MKrysz/POV_Display/POV_display_code/Core/Inc/clk.h

#ifndef A386B258_FA04_44B2_AE7A_AE9C989B530D
#define A386B258_FA04_44B2_AE7A_AE9C989B530D

const uint8_t hours[8] = {0b00000000, 0b00000000, 0b00000000, 0b00000000, 0b00000000, 0b00100001, 0b01001000, 0b10010010};

const uint8_t minutes[8] = {0b00000000, 0b00000000, 0b00000000, 0b10010010, 0b00100101, 0b01001000, 0b10010010, 0b00100101};

const uint8_t seconds[8] = {0b00100101, 0b01001000, 0b10010010, 0b00100101, 0b01001000, 0b10010010, 0b00100101, 0b01001000};

const uint8_t CLK_BKGD[120][8] = {
{0b00000000, 0b00000000, 0b00000000, 0b00000000, 0b00000000, 0b00000000, 0b00000000, 0b00000000},
{0b11100000, 0b11000001, 0b00000000, 0b00000000, 0b00000000, 0b00000000, 0b00000000, 0b00000000},
{0b00011100, 0b11111001, 0b00000000, 0b00000000, 0b00000000, 0b00000000, 0b00000000, 0b00000000},
{0b00011101, 0b11000111, 0b00000000, 0b00000000, 0b00000000, 0b00000000, 0b00000000, 0b00000000},
{0b11100000, 0b11000001, 0b00000000, 0b00000000, 0b00000000, 0b00000000, 0b00000000, 0b00000000},
{0b00000000, 0b00000000, 0b00000000, 0b00000000, 0b00000000, 0b00000000, 0b00000000, 0b00000000},
{0b00000000, 0b00000000, 0b00000000, 0b00000000, 0b00000000, 0b00000000, 0b00000000, 0b00000000},
{0b00000000, 0b00000000, 0b00000000, 0b00000000, 0b00000000, 0b00000000, 0b00000000, 0b00000000},
{0b00000000, 0b00000000, 0b00000000, 0b00000000, 0b00000000, 0b00000000, 0b00000000, 0b00000000},
{0b11100000, 0b00000000, 0b00000000, 0b00000000, 0b00000000, 0b00000000, 0b00000000, 0b00000000},
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
{0b00000000, 0b00000000, 0b00000000, 0b00000000, 0b00000000, 0b00000000, 0b00000000, 0b00000000},
{0b11111101, 0b11111111, 0b00000000, 0b00000000, 0b00000000, 0b00000000, 0b00000000, 0b00000000},
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
};



#endif /* A386B258_FA04_44B2_AE7A_AE9C989B530D */
