MKrysz/POV_Display/POV_display_code/Core/Inc/config.h

#ifndef C484BAE8_510C_4F08_8290_32E19870EC4C
#define C484BAE8_510C_4F08_8290_32E19870EC4C

#define MODE_IMAGE
// #define MODE_ANALOG_CLOCK

#define SHUTDOWN_ENABLE 1

#endif /* C484BAE8_510C_4F08_8290_32E19870EC4C */
