MKrysz/POV_Display/POV_display_code/Core/Src/gpio.c

/**
  ******************************************************************************
  * @file    gpio.c
  * @brief   This file provides code for the configuration
  *          of all used GPIO pins.
  ******************************************************************************
  * @attention
  *
  * <h2><center>&copy; Copyright (c) 2022 STMicroelectronics.
  * All rights reserved.</center></h2>
  *
  * This software component is licensed by ST under BSD 3-Clause license,
  * the "License"; You may not use this file except in compliance with the
  * License. You may obtain a copy of the License at:
  *                        opensource.org/licenses/BSD-3-Clause
  *
  ******************************************************************************
  */

/* Includes ------------------------------------------------------------------*/
#include "gpio.h"

/* USER CODE BEGIN 0 */
#include <stdbool.h>
#include "tim.h"
#include "led.h"
#include "array.h"
#include "main.h"
#include "config.h"
/* USER CODE END 0 */

/*----------------------------------------------------------------------------*/
/* Configure GPIO                                                             */
/*----------------------------------------------------------------------------*/
/* USER CODE BEGIN 1 */
/*externs*/
extern volatile uint16_t period;
extern volatile uint16_t periodUS;
extern volatile size_t imgIdx;
extern volatile bool isShutDown;

/*variables*/

volatile bool GPIO_Flag = false;
/* USER CODE END 1 */

/** Configure pins as
        * Analog
        * Input
        * Output
        * EVENT_OUT
        * EXTI
*/
void MX_GPIO_Init(void)
{

  GPIO_InitTypeDef GPIO_InitStruct = {0};

  /* GPIO Ports Clock Enable */
  __HAL_RCC_GPIOC_CLK_ENABLE();
  __HAL_RCC_GPIOA_CLK_ENABLE();
  __HAL_RCC_GPIOB_CLK_ENABLE();

  /*Configure GPIO pin Output Level */
  HAL_GPIO_WritePin(GPIOA, BAT_EN_Pin|NOT_OE_Pin|NOT_CLEAR_Pin, GPIO_PIN_RESET);

  /*Configure GPIO pin Output Level */
  HAL_GPIO_WritePin(RCLK_GPIO_Port, RCLK_Pin, GPIO_PIN_RESET);

  /*Configure GPIO pin : PtPin */
  GPIO_InitStruct.Pin = FDBK_Pin;
  GPIO_InitStruct.Mode = GPIO_MODE_IT_RISING;
  GPIO_InitStruct.Pull = GPIO_NOPULL;
  HAL_GPIO_Init(FDBK_GPIO_Port, &GPIO_InitStruct);

  /*Configure GPIO pins : PAPin PAPin PAPin */
  GPIO_InitStruct.Pin = BAT_EN_Pin|NOT_OE_Pin|NOT_CLEAR_Pin;
  GPIO_InitStruct.Mode = GPIO_MODE_OUTPUT_PP;
  GPIO_InitStruct.Pull = GPIO_NOPULL;
  GPIO_InitStruct.Speed = GPIO_SPEED_FREQ_LOW;
  HAL_GPIO_Init(GPIOA, &GPIO_InitStruct);

  /*Configure GPIO pin : PtPin */
  GPIO_InitStruct.Pin = RCLK_Pin;
  GPIO_InitStruct.Mode = GPIO_MODE_OUTPUT_PP;
  GPIO_InitStruct.Pull = GPIO_NOPULL;
  GPIO_InitStruct.Speed = GPIO_SPEED_FREQ_LOW;
  HAL_GPIO_Init(RCLK_GPIO_Port, &GPIO_InitStruct);

  /*Configure GPIO pin : PtPin */
  GPIO_InitStruct.Pin = USB_FLAG_Pin;
  GPIO_InitStruct.Mode = GPIO_MODE_INPUT;
  GPIO_InitStruct.Pull = GPIO_NOPULL;
  HAL_GPIO_Init(USB_FLAG_GPIO_Port, &GPIO_InitStruct);

  /* EXTI interrupt init*/
  HAL_NVIC_SetPriority(EXTI4_15_IRQn, 0, 0);
  HAL_NVIC_EnableIRQ(EXTI4_15_IRQn);

}

/* USER CODE BEGIN 2 */

void GPIO_Init(){
}

void HAL_GPIO_EXTI_Callback(uint16_t GPIO_Pin){
  GPIO_Flag = true;
  #if SHUTDOWN_ENABLE
  if(isShutDown)
    wakeUpRoutine();
  #endif
  

  periodUS = __HAL_TIM_GET_COUNTER(&HTIM_US_GET);
  __HAL_TIM_SET_COUNTER(&HTIM_US_GET,0);

  // anchor the image
  imgIdx = 0;
}
/* USER CODE END 2 */

/************************ (C) COPYRIGHT STMicroelectronics *****END OF FILE****/
