MKrysz/POV_Display/POV_display_code/Core/Src/rtc.c

/**
  ******************************************************************************
  * @file    rtc.c
  * @brief   This file provides code for the configuration
  *          of the RTC instances.
  ******************************************************************************
  * @attention
  *
  * <h2><center>&copy; Copyright (c) 2022 STMicroelectronics.
  * All rights reserved.</center></h2>
  *
  * This software component is licensed by ST under BSD 3-Clause license,
  * the "License"; You may not use this file except in compliance with the
  * License. You may obtain a copy of the License at:
  *                        opensource.org/licenses/BSD-3-Clause
  *
  ******************************************************************************
  */

/* Includes ------------------------------------------------------------------*/
#include "rtc.h"

RTC_HandleTypeDef hrtc;

/* RTC init function */
void MX_RTC_Init(void)
{

  RTC_TimeTypeDef sTime = {0};
  RTC_DateTypeDef sDate = {0};

  /** Initialize RTC Only
  */
  hrtc.Instance = RTC;
  hrtc.Init.HourFormat = RTC_HOURFORMAT_12;
  hrtc.Init.AsynchPrediv = 127;
  hrtc.Init.SynchPrediv = 255;
  hrtc.Init.OutPut = RTC_OUTPUT_DISABLE;
  hrtc.Init.OutPutRemap = RTC_OUTPUT_REMAP_NONE;
  hrtc.Init.OutPutPolarity = RTC_OUTPUT_POLARITY_HIGH;
  hrtc.Init.OutPutType = RTC_OUTPUT_TYPE_OPENDRAIN;
  if (HAL_RTC_Init(&hrtc) != HAL_OK)
  {
    Error_Handler();
  }

  /* USER CODE BEGIN Check_RTC_BKUP */

  //set my time
  sTime.Hours = 0x08;
  sTime.Minutes = 0x30;
  sTime.Seconds = 0x00;
  sTime.TimeFormat = RTC_HOURFORMAT12_PM;
  sTime.DayLightSaving = RTC_DAYLIGHTSAVING_NONE;
  sTime.StoreOperation = RTC_STOREOPERATION_RESET;
  if (HAL_RTC_SetTime(&hrtc, &sTime, RTC_FORMAT_BCD) != HAL_OK)
  {
    Error_Handler();
  }
  sDate.WeekDay = RTC_WEEKDAY_WEDNESDAY;
  sDate.Month = RTC_MONTH_MAY;
  sDate.Date = 0x25;
  sDate.Year = 0x22;

  if (HAL_RTC_SetDate(&hrtc, &sDate, RTC_FORMAT_BCD) != HAL_OK)
  {
    Error_Handler();
  }

  return;

  /* USER CODE END Check_RTC_BKUP */

  /** Initialize RTC and set the Time and Date
  */
  sTime.Hours = 0x3;
  sTime.Minutes = 0x30;
  sTime.Seconds = 0x45;
  sTime.TimeFormat = RTC_HOURFORMAT12_PM;
  sTime.DayLightSaving = RTC_DAYLIGHTSAVING_NONE;
  sTime.StoreOperation = RTC_STOREOPERATION_RESET;
  if (HAL_RTC_SetTime(&hrtc, &sTime, RTC_FORMAT_BCD) != HAL_OK)
  {
    Error_Handler();
  }
  sDate.WeekDay = RTC_WEEKDAY_THURSDAY;
  sDate.Month = RTC_MONTH_APRIL;
  sDate.Date = 0x21;
  sDate.Year = 0x0;

  if (HAL_RTC_SetDate(&hrtc, &sDate, RTC_FORMAT_BCD) != HAL_OK)
  {
    Error_Handler();
  }
}

void HAL_RTC_MspInit(RTC_HandleTypeDef* rtcHandle)
{

  if(rtcHandle->Instance==RTC)
  {
    /* RTC clock enable */
    __HAL_RCC_RTC_ENABLE();
  }
}

void HAL_RTC_MspDeInit(RTC_HandleTypeDef* rtcHandle)
{

  if(rtcHandle->Instance==RTC)
  {
    /* Peripheral clock disable */
    __HAL_RCC_RTC_DISABLE();
  }
}

/************************ (C) COPYRIGHT STMicroelectronics *****END OF FILE****/
