MKrysz/POV_Display/POV_display_code/Core/Inc/img.h

#define IMG_SIZE 6

const uint8_t image[6][8] = {
{0b01001000, 0b10010010, 0b00100101, 0b01001000, 0b10010010, 0b00100101, 0b01001000, 0b10010010},
{0b11011000, 0b10110111, 0b01101101, 0b11011010, 0b10110111, 0b01101101, 0b11011010, 0b10110111},
{0b10010000, 0b00100101, 0b01001000, 0b10010010, 0b00100101, 0b01001000, 0b10010010, 0b00100101},
{0b10110101, 0b01101101, 0b11011010, 0b10110111, 0b01101101, 0b11011010, 0b10110111, 0b01101101},
{0b00100101, 0b01001000, 0b10010010, 0b00100101, 0b01001000, 0b10010010, 0b00100101, 0b01001000},
{0b01101101, 0b11011010, 0b10110111, 0b01101101, 0b11011010, 0b10110111, 0b01101101, 0b11011010}
};
